FrankRubandamayonzaMagezi/LED-Bulb-PCB-Design-and-Development/images/Board.jpeg

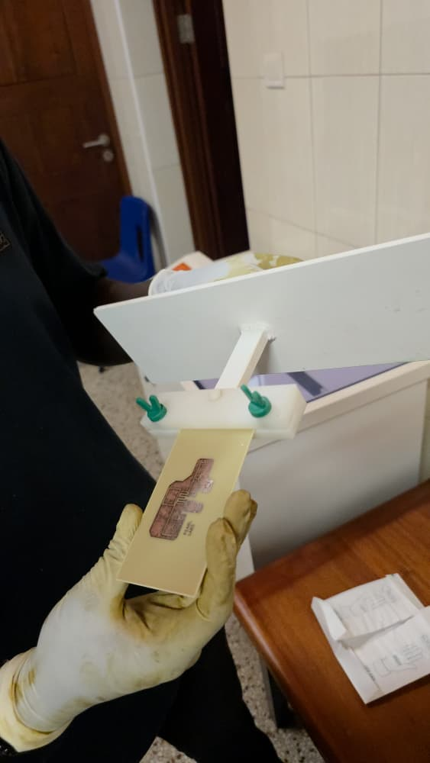
images/Board.jpeg
