FrankRubandamayonzaMagezi/LED-Bulb-PCB-Design-and-Development/images/Digital_Oscilloscope_Output.png

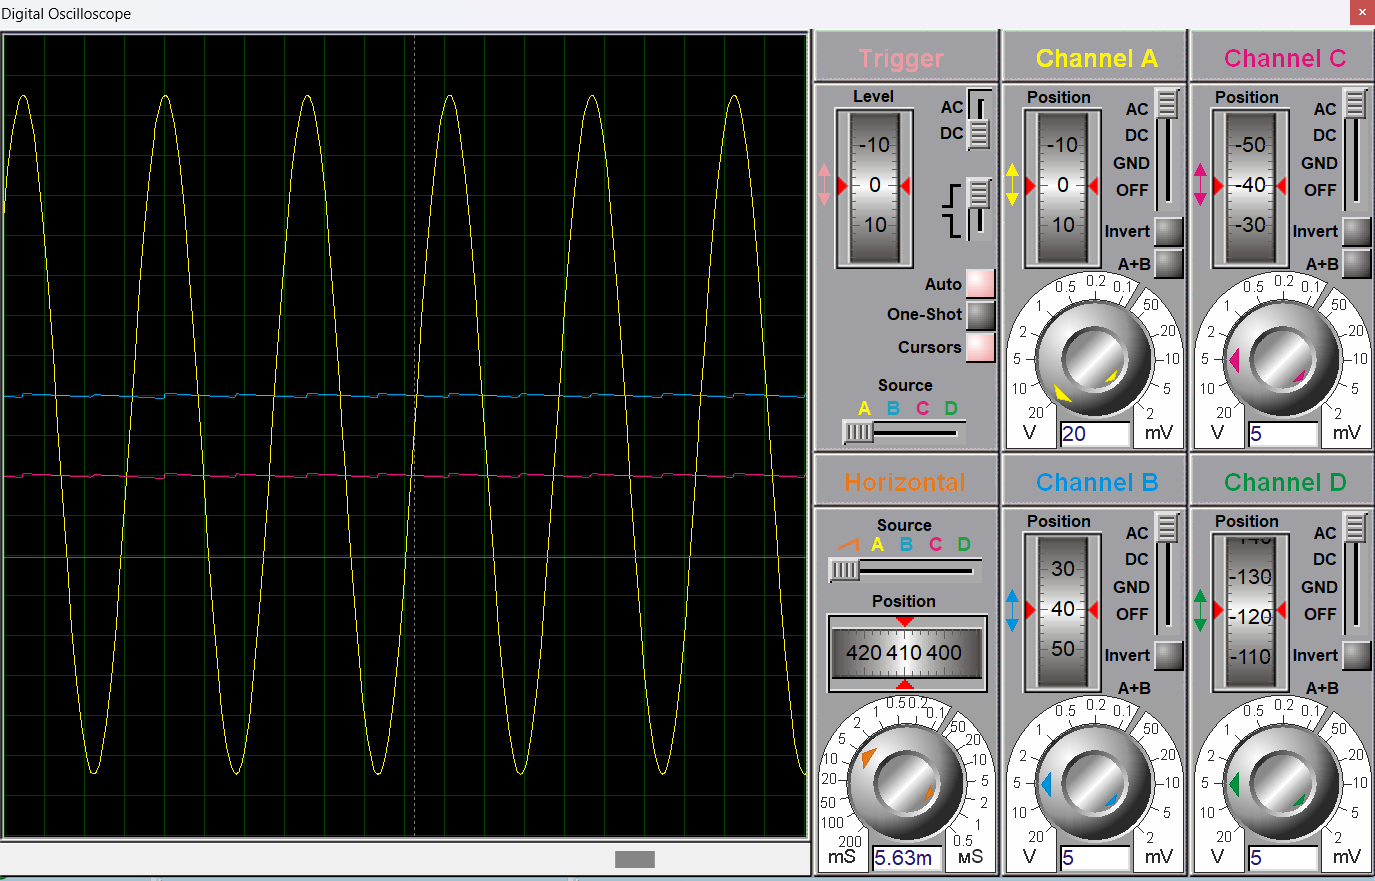
images/Digital_Oscilloscope_Output.png
