FrankRubandamayonzaMagezi/LED-Bulb-PCB-Design-and-Development/fabrication/pore_fluid.jpeg

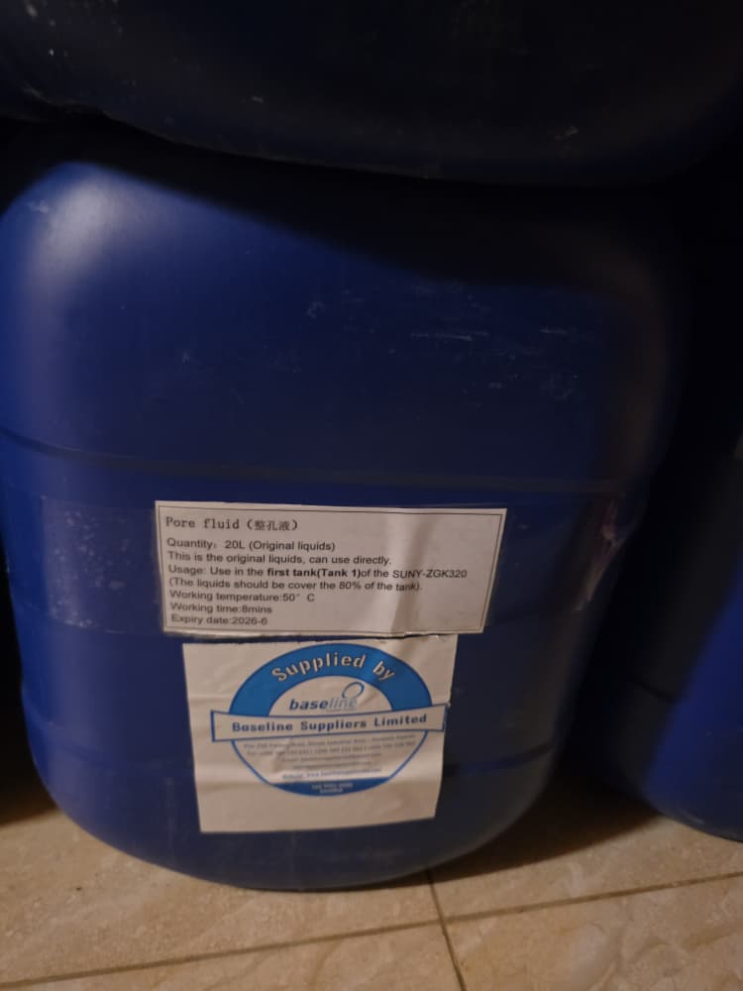
fabrication/pore_fluid.jpeg
